Nullkraft/6GHz-Signal-Generator/Summary_30June2020/MAX2871_Sweep_1200-1500_401pts_1ms_FracOpt-Beta.png

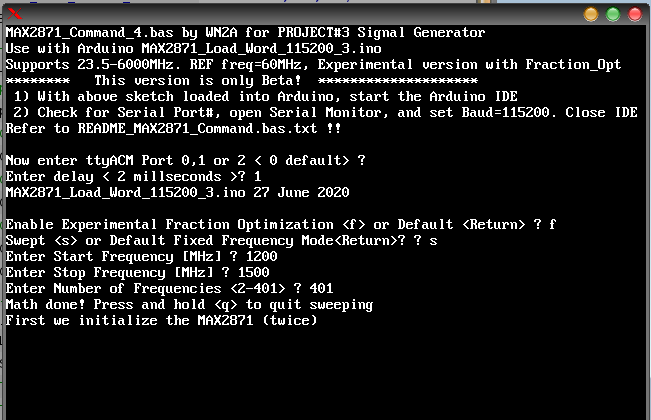
Summary_30June2020/MAX2871_Sweep_1200-1500_401pts_1ms_FracOpt-Beta.png
