Nullkraft/6GHz-Signal-Generator/Test_Data_27June2020/Timing_MAX2871_Sweep_1200-1500MHz_401pts_1ms_DefaultFrac.jpg

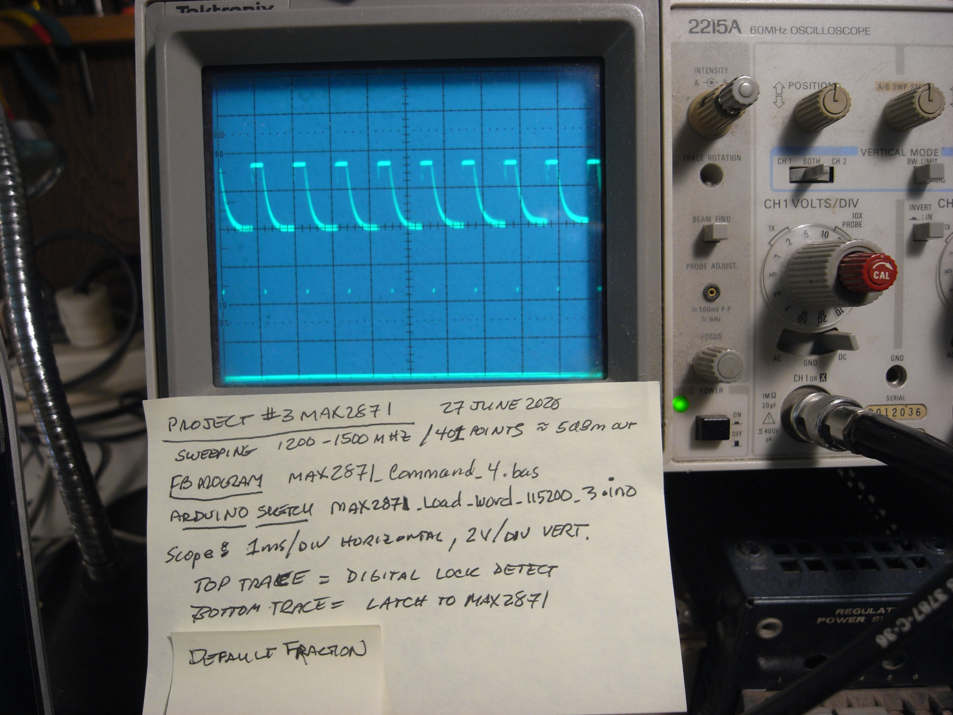
Test_Data_27June2020/Timing_MAX2871_Sweep_1200-1500MHz_401pts_1ms_DefaultFrac.jpg
